maxstrauch/kim-uno/images/backshot.jpg

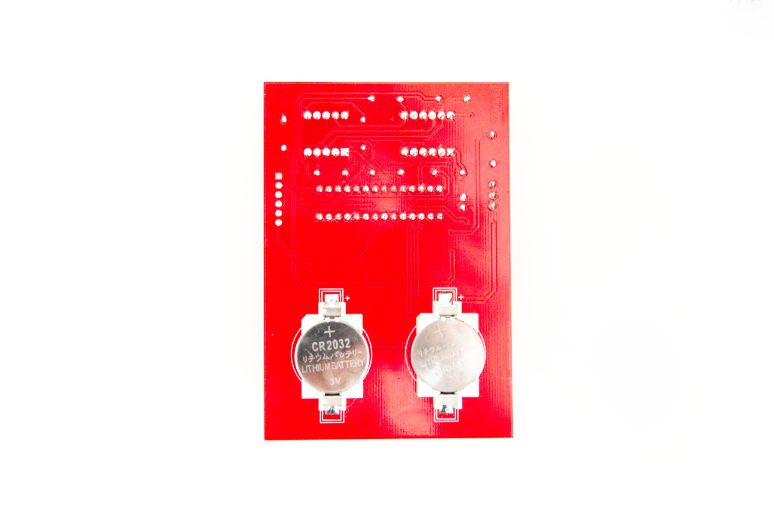
images/backshot.jpg
