maxstrauch/kim-uno/images/family_shot.jpg

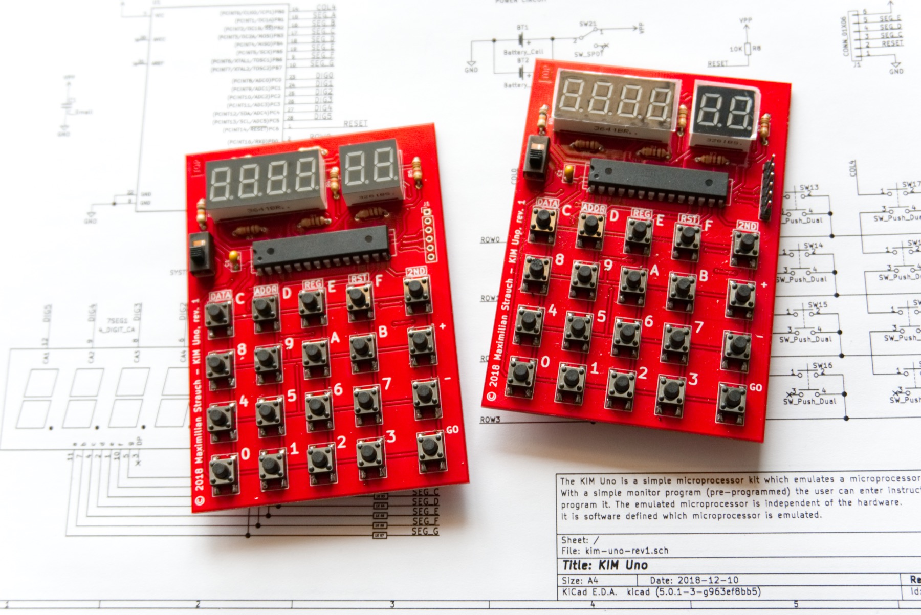
images/family_shot.jpg
