maxstrauch/kim-uno/images/finished_batteries.jpg

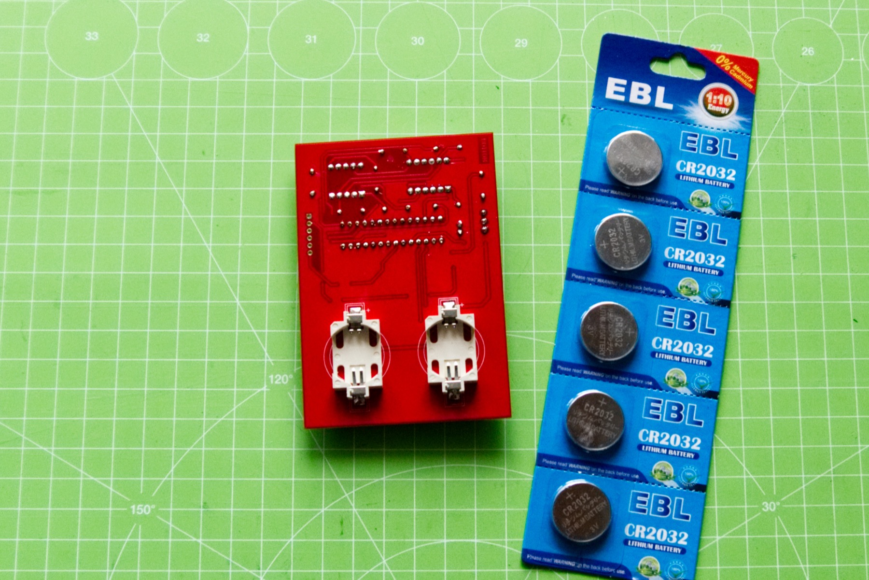
images/finished_batteries.jpg
