maxstrauch/kim-uno/images/finished_product.jpg

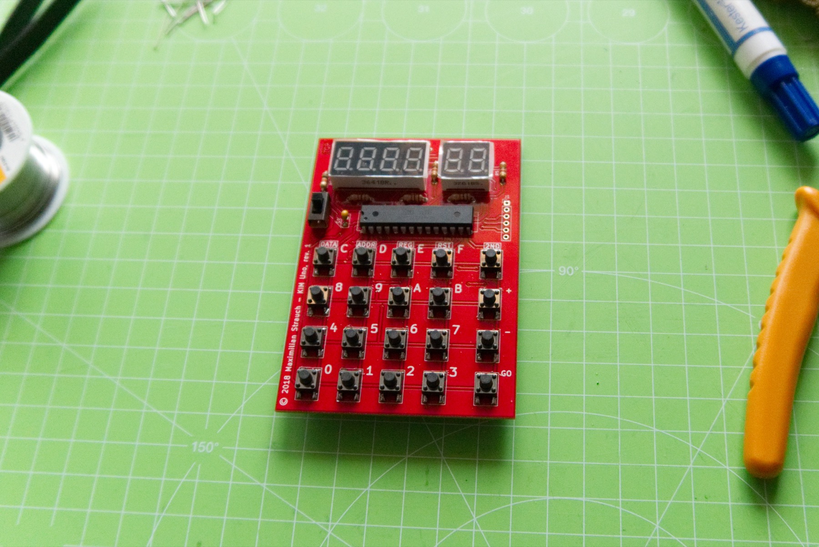
images/finished_product.jpg
