maxstrauch/kim-uno/images/frontshot.jpg

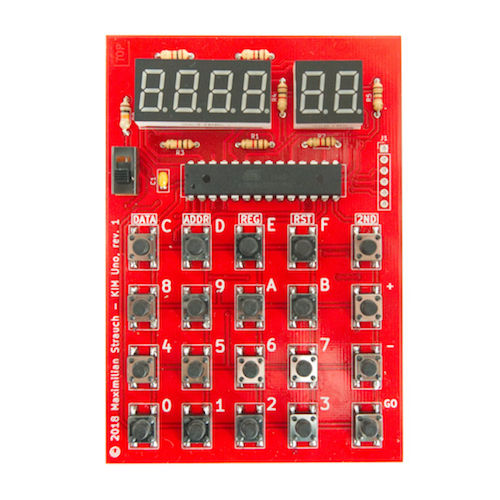
images/frontshot.jpg
