maxstrauch/kim-uno/images/frontshot_bg-plans.jpg

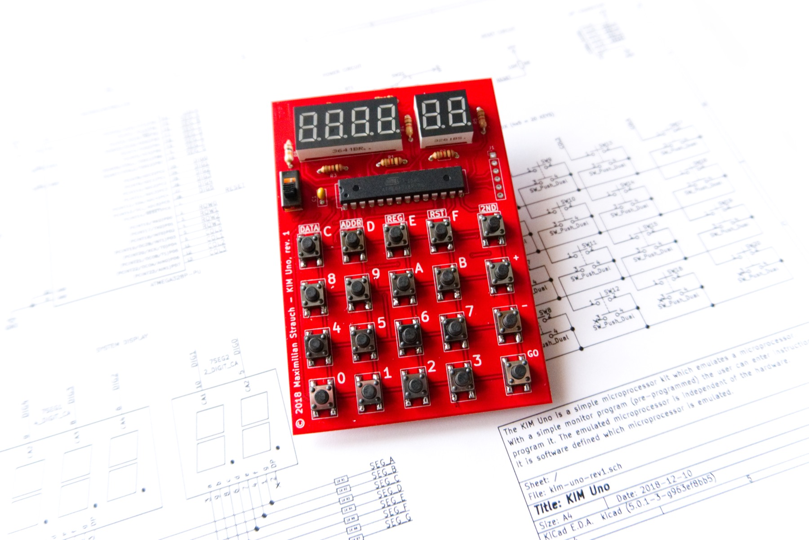
images/frontshot_bg-plans.jpg
