maxstrauch/kim-uno/images/frontshot_with_booklet2.jpg

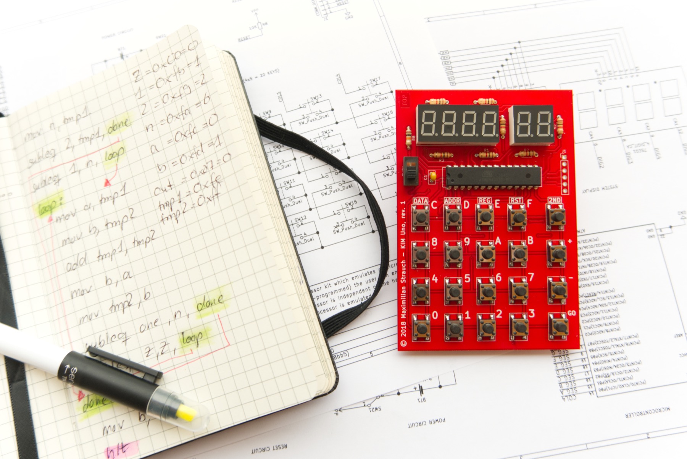
images/frontshot_with_booklet2.jpg
