maxstrauch/kim-uno/images/frontshot_with_booklet.jpg

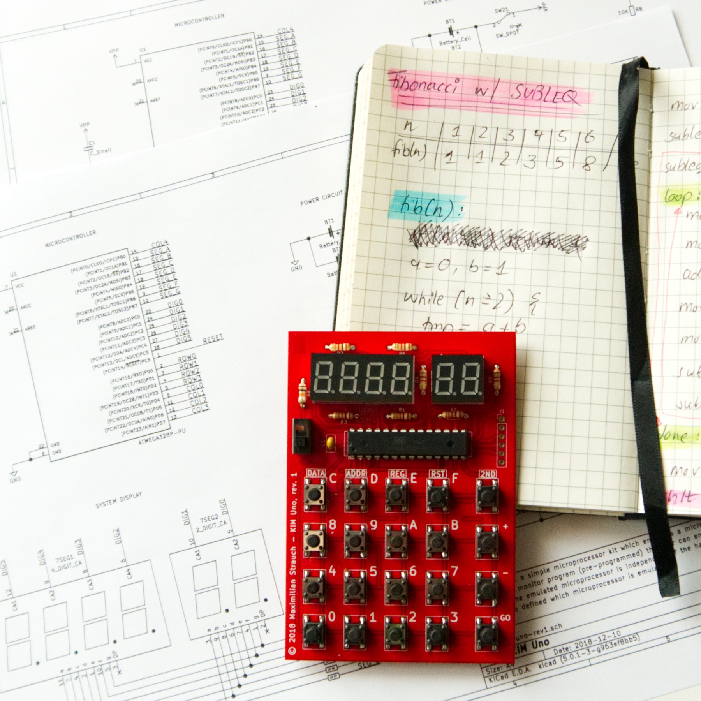
images/frontshot_with_booklet.jpg
