maxstrauch/kim-uno/images/isp_programming.jpg

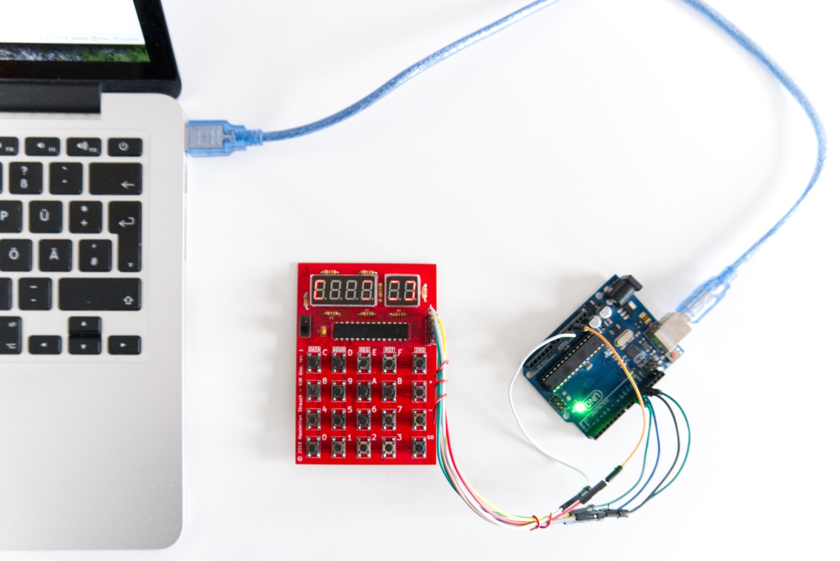
images/isp_programming.jpg
