maxstrauch/kim-uno/images/isp_programming_trick.jpg

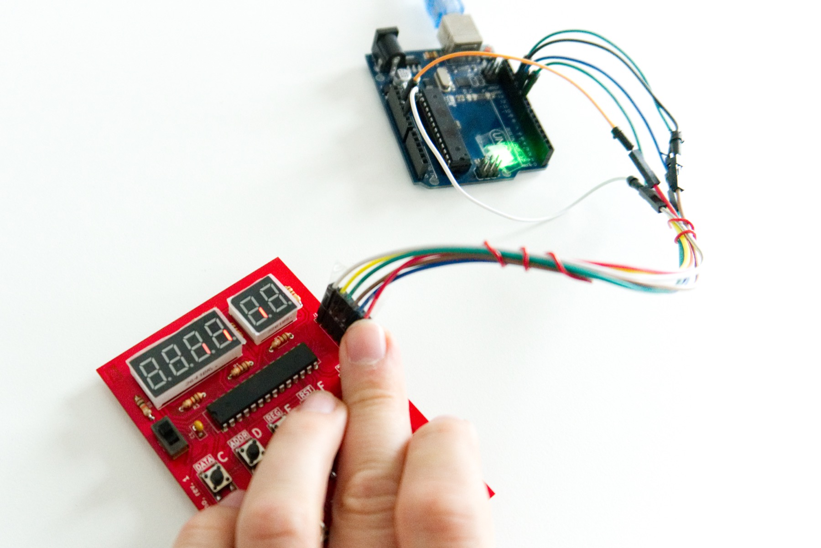
images/isp_programming_trick.jpg
