maxstrauch/kim-uno/images/kim-uno-rev1-schematic.png

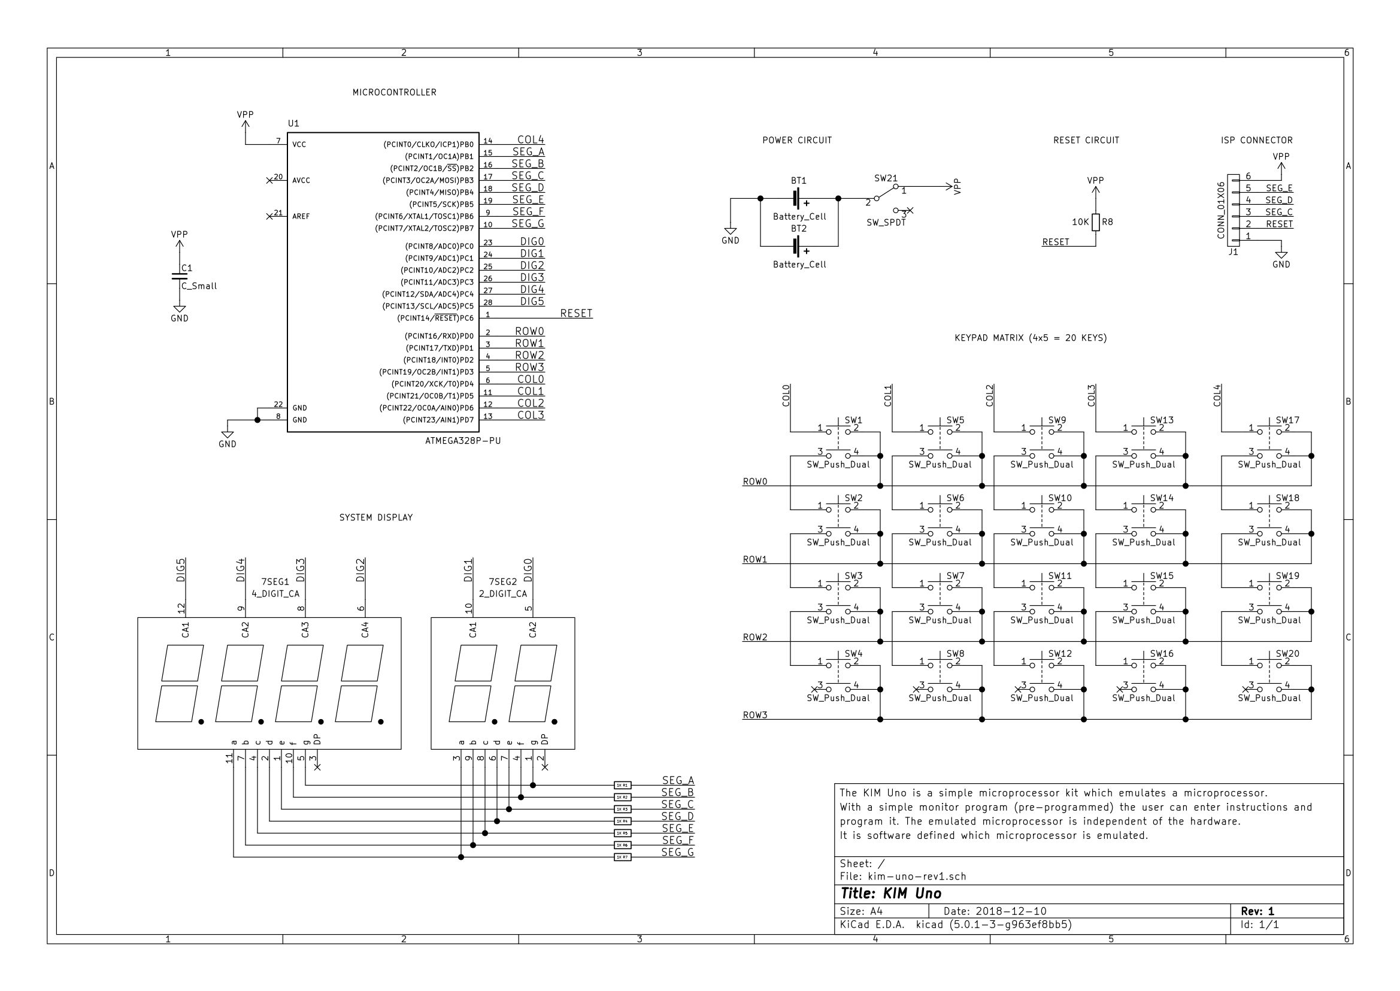
images/kim-uno-rev1-schematic.png
