maxstrauch/kim-uno/images/main-title.jpg

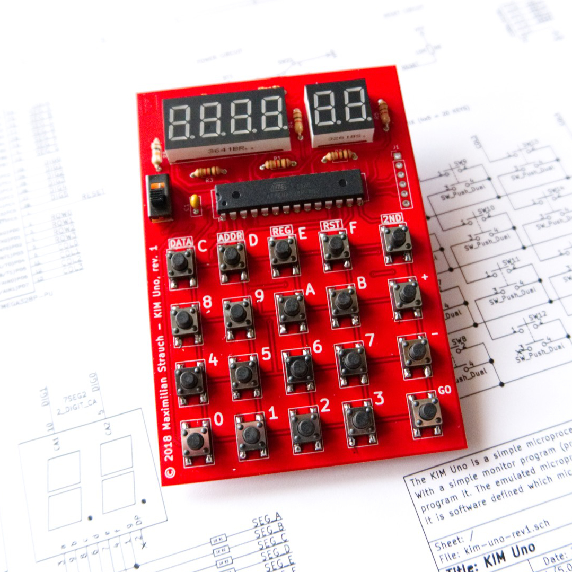
images/main-title.jpg
