maxstrauch/kim-uno/images/pcb.jpg

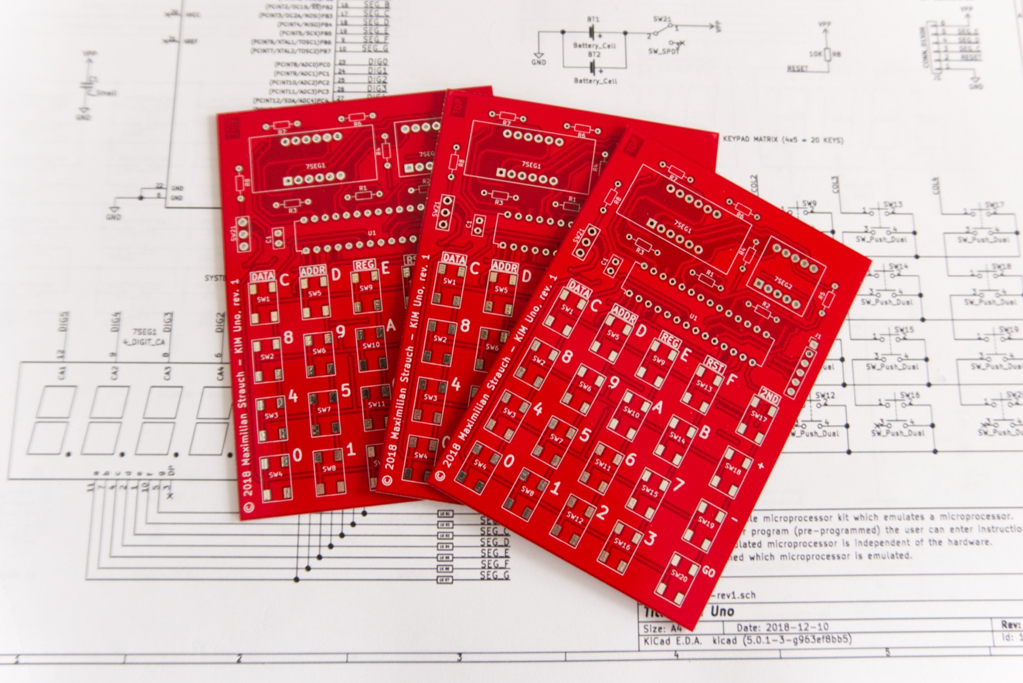
images/pcb.jpg
