maxstrauch/kim-uno/images/screenshot_kicad.png

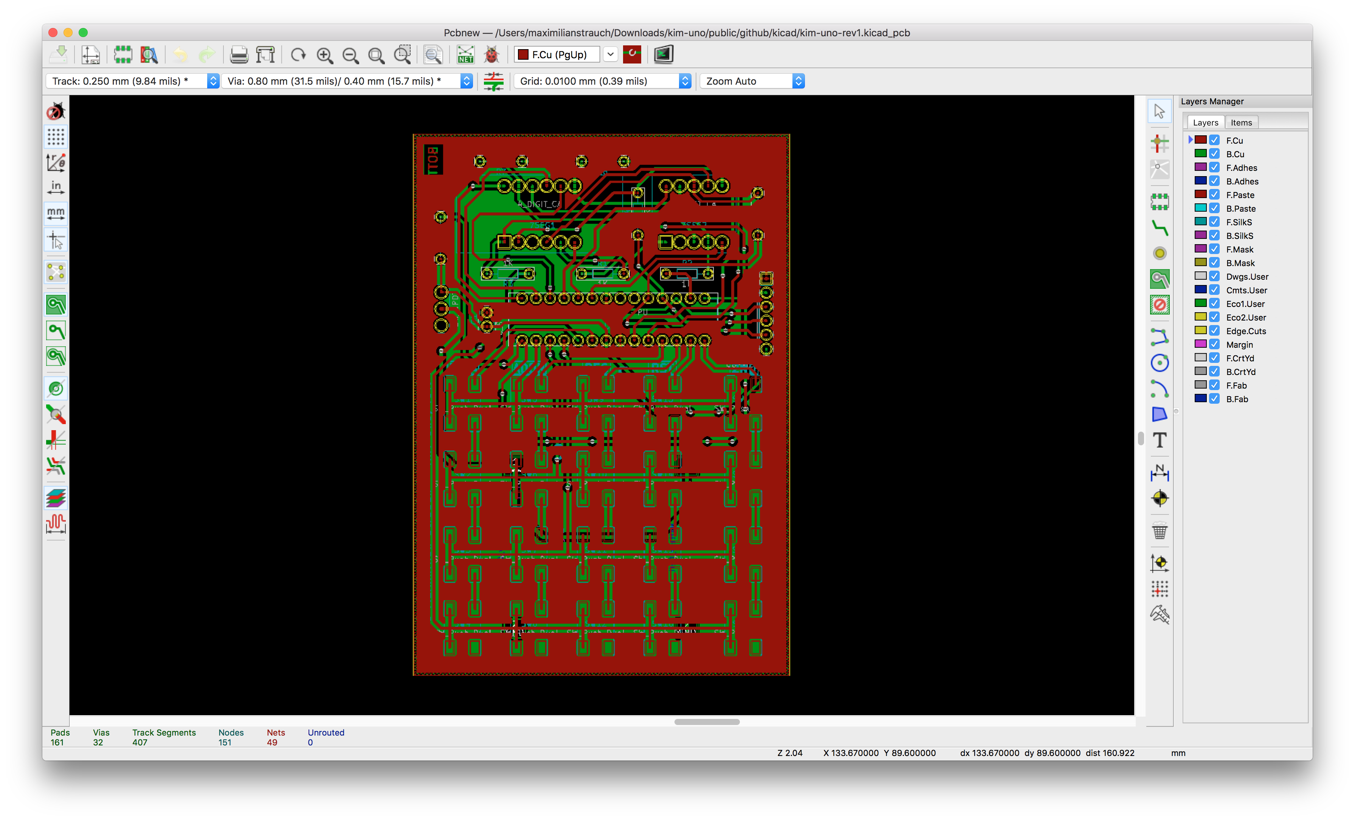
images/screenshot_kicad.png
