maxstrauch/kim-uno/images/tools.jpg

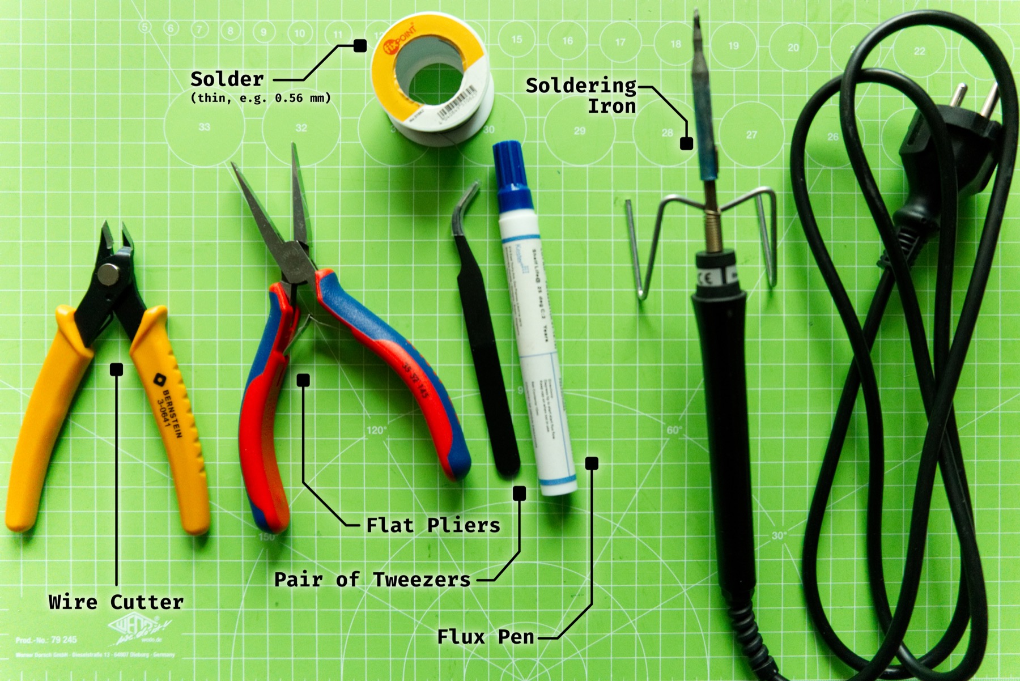
images/tools.jpg
