maxstrauch/kim-uno/kicad/datasheets/B3F-Tact-Switch-6x6x4-3-1000PCS-LOT-push-button-switch-5-6-7-8-9-10.jpg

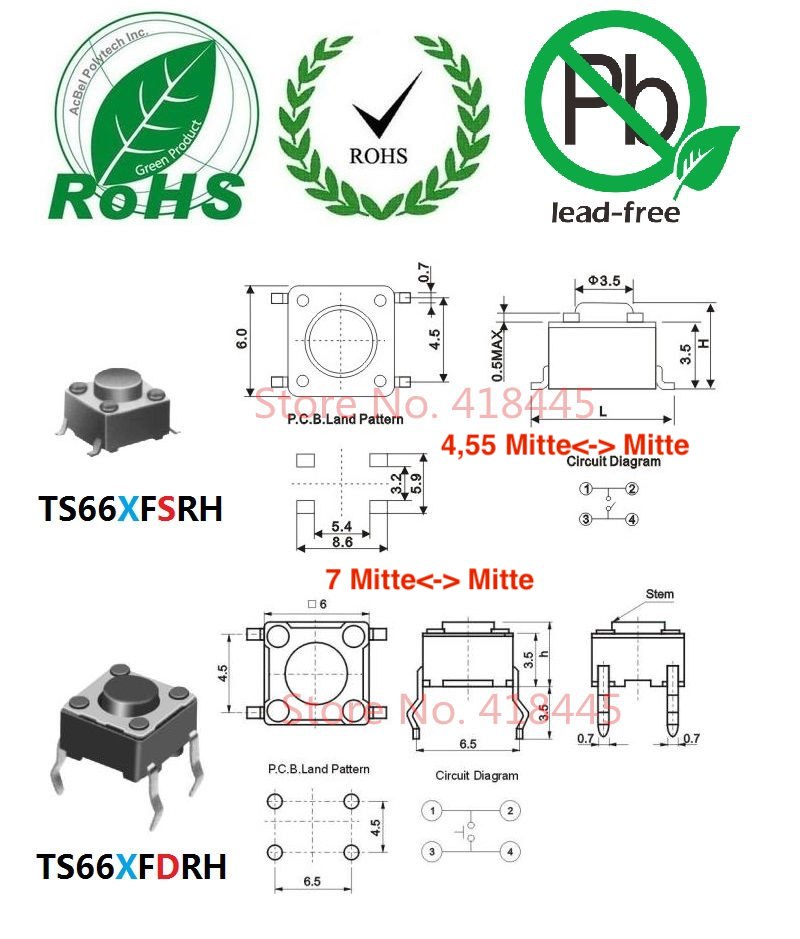
kicad/datasheets/B3F-Tact-Switch-6x6x4-3-1000PCS-LOT-push-button-switch-5-6-7-8-9-10.jpg
