maxstrauch/kim-uno/kicad/datasheets/The-toggle-switch-SS12F17G3-factory-direct-slide-switch-electronic-switch.jpg

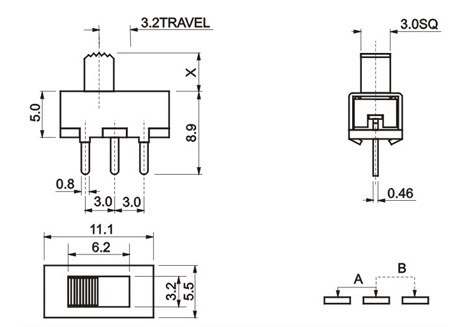
kicad/datasheets/The-toggle-switch-SS12F17G3-factory-direct-slide-switch-electronic-switch.jpg
