maxstrauch/kim-uno/kicad/datasheets/Z1561605.jpg

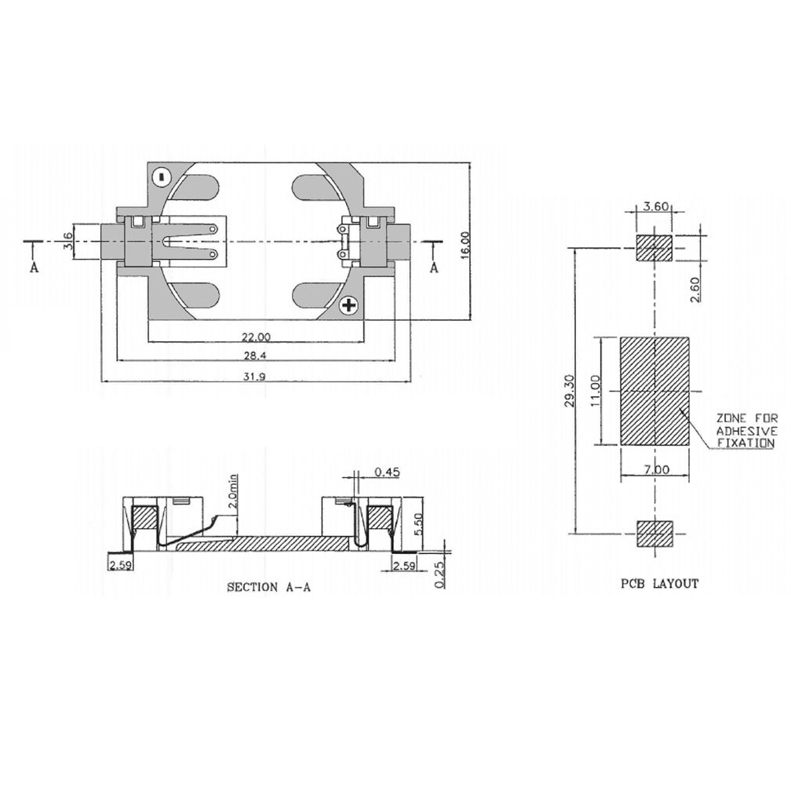
kicad/datasheets/Z1561605.jpg
