maxstrauch/kim-uno/images/step1_resistors.jpg

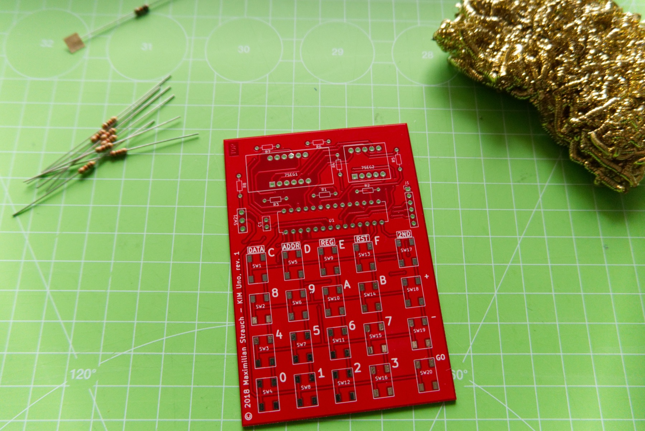
images/step1_resistors.jpg
