maxstrauch/kim-uno/images/step1a_bend_resistors_over.jpg

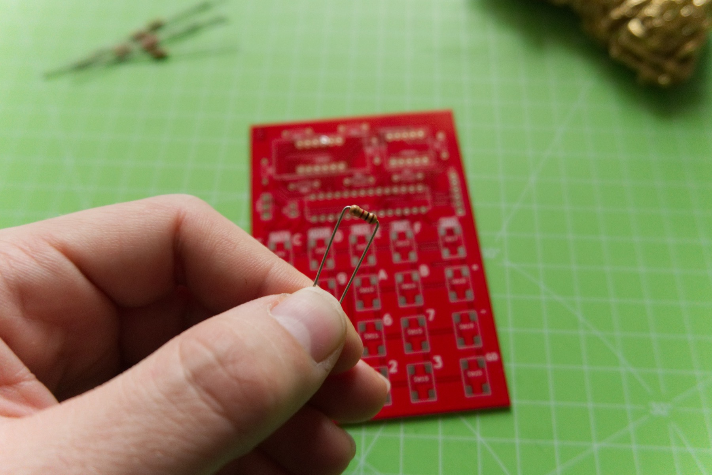
images/step1a_bend_resistors_over.jpg
