maxstrauch/kim-uno/images/step1b_insert_resistors.jpg

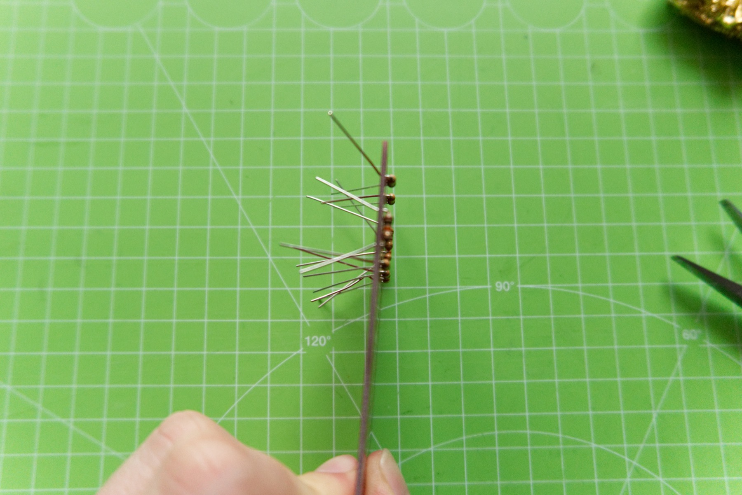
images/step1b_insert_resistors.jpg
