maxstrauch/kim-uno/images/step1c_cut_wires.jpg

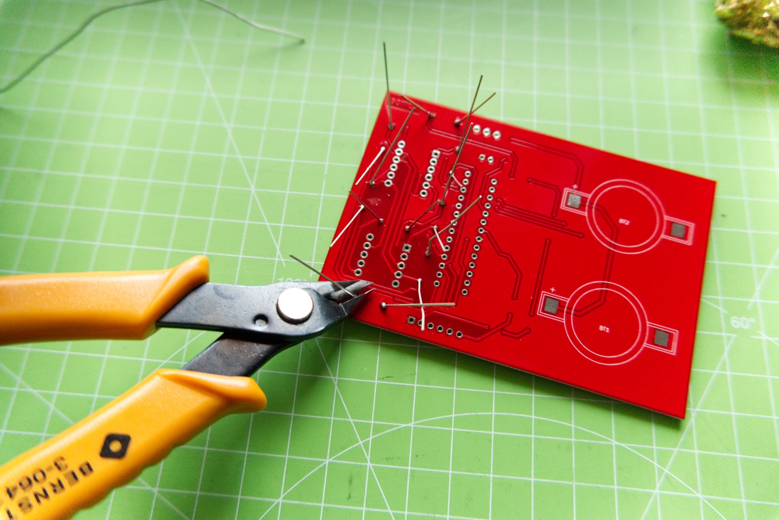
images/step1c_cut_wires.jpg
