maxstrauch/kim-uno/images/step2_assemble_switches.jpg

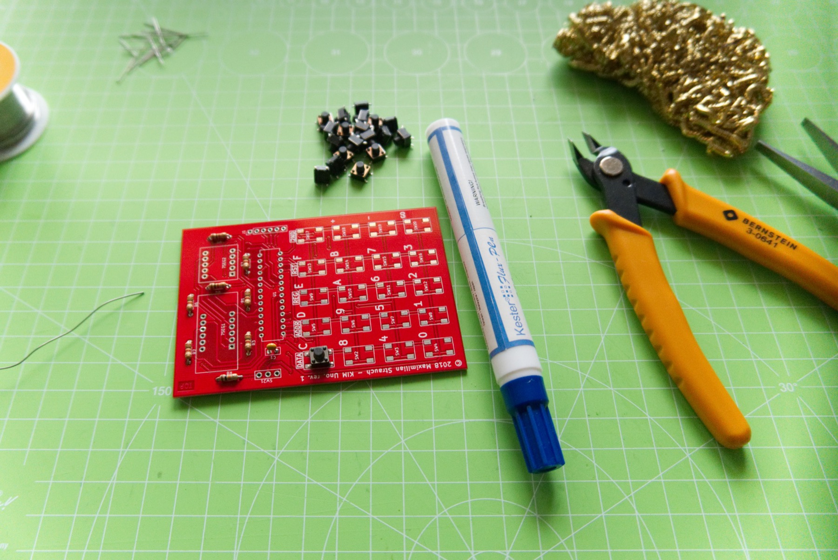
images/step2_assemble_switches.jpg
