maxstrauch/kim-uno/images/step2b_tac_switches_w_labels.jpg

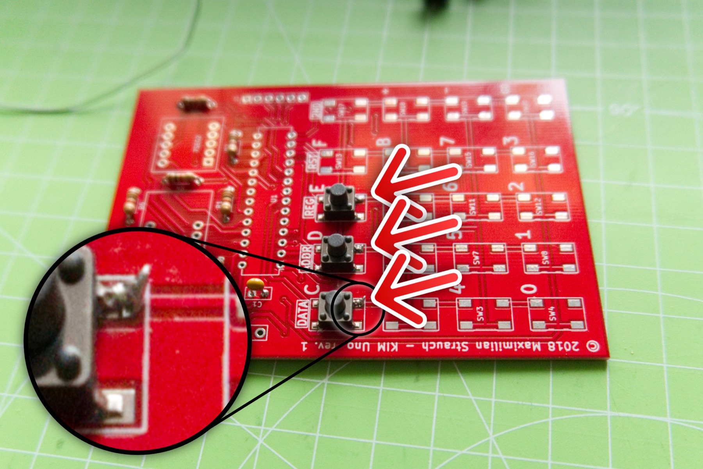
images/step2b_tac_switches_w_labels.jpg
