maxstrauch/kim-uno/images/step2c_finished.jpg

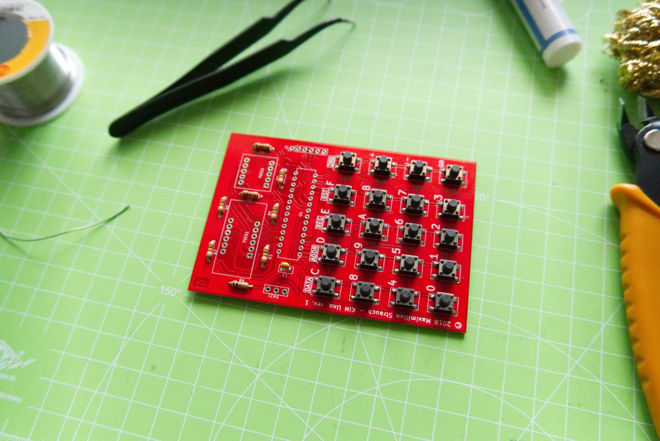
images/step2c_finished.jpg
