maxstrauch/kim-uno/images/step5_install_seven_segment_tac_w_label.jpg

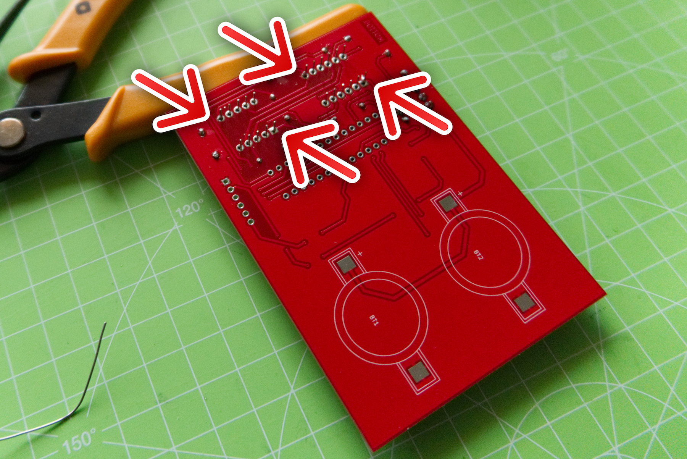
images/step5_install_seven_segment_tac_w_label.jpg
