maxstrauch/kim-uno/images/step5b_then_solder_the_rest.jpg

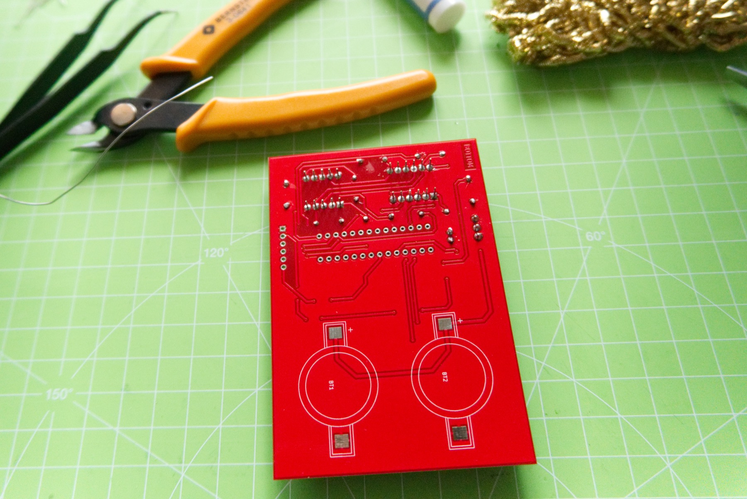
images/step5b_then_solder_the_rest.jpg
