maxstrauch/kim-uno/images/step6_add_battery_holders.jpg

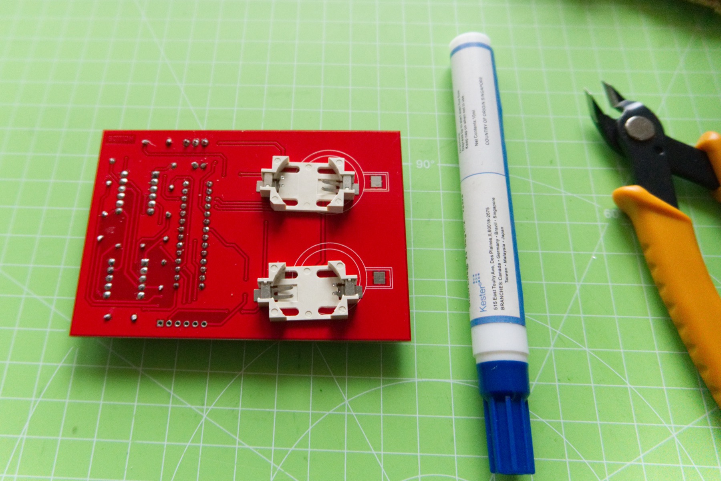
images/step6_add_battery_holders.jpg
