maxstrauch/kim-uno/src/fibonacci.h

/*
 --- Report ---
  Program starts at: 0x0a
  Code length: 96 bytes

  Variables:
   - z at 0x00 (initial value: 0)
   - n at 0xfa (initial value: 6)
   - a at 0xfc (initial value: 0)
   - b at 0xfd (initial value: 1)
   - out at 0x07 (initial value: 0)
   - tmp1 at 0xfe (initial value: 0)
   - tmp2 at 0xff (initial value: 0)
   - one at 0xfb (initial value: 1)
   - two at 0xf9 (initial value: 2)

  Labels:
   - loop at 28
   - done at 91
*/

unsigned const PROGMEM char prg[256] = {
/*        0x00  0x01  0x02  0x03  0x04  0x05  0x06  0x07  0x08  0x09  0x0a  0x0b  0x0c  0x0d  0x0e  0x0f  */
/*0x00*/  0x00, 0x00, 0x00, 0x00, 0x00, 0x00, 0x00, 0x00, 0x00, 0x00, 0xfe, 0xfe, 0x0d, 0xfa, 0x00, 0x10, 
/*0x10*/  0x00, 0xfe, 0x13, 0x00, 0x00, 0x16, 0xf9, 0xfe, 0x5b, 0xfb, 0xfa, 0x1c, 0xfe, 0xfe, 0x1f, 0xfc, 
/*0x20*/  0x00, 0x22, 0x00, 0xfe, 0x25, 0x00, 0x00, 0x28, 0xff, 0xff, 0x2b, 0xfd, 0x00, 0x2e, 0x00, 0xff, 
/*0x30*/  0x31, 0x00, 0x00, 0x34, 0xfe, 0x00, 0x37, 0x00, 0xff, 0x3a, 0x00, 0x00, 0x3d, 0xfc, 0xfc, 0x40, 
/*0x40*/  0xfd, 0x00, 0x43, 0x00, 0xfc, 0x46, 0x00, 0x00, 0x49, 0xfd, 0xfd, 0x4c, 0xff, 0x00, 0x4f, 0x00, 
/*0x50*/  0xfd, 0x52, 0x00, 0x00, 0x55, 0xfb, 0xfa, 0x5b, 0x00, 0x00, 0x1c, 0x07, 0x07, 0x5e, 0xfd, 0x00, 
/*0x60*/  0x61, 0x00, 0x07, 0x64, 0x00, 0x00, 0x67, 0x00, 0x00, 0xff, 0x00, 0x00, 0x00, 0x00, 0x00, 0x00, 
/*0x70*/  0x00, 0x00, 0x00, 0x00, 0x00, 0x00, 0x00, 0x00, 0x00, 0x00, 0x00, 0x00, 0x00, 0x00, 0x00, 0x00, 
/*0x80*/  0x00, 0x00, 0x00, 0x00, 0x00, 0x00, 0x00, 0x00, 0x00, 0x00, 0x00, 0x00, 0x00, 0x00, 0x00, 0x00, 
/*0x90*/  0x00, 0x00, 0x00, 0x00, 0x00, 0x00, 0x00, 0x00, 0x00, 0x00, 0x00, 0x00, 0x00, 0x00, 0x00, 0x00, 
/*0xa0*/  0x00, 0x00, 0x00, 0x00, 0x00, 0x00, 0x00, 0x00, 0x00, 0x00, 0x00, 0x00, 0x00, 0x00, 0x00, 0x00, 
/*0xb0*/  0x00, 0x00, 0x00, 0x00, 0x00, 0x00, 0x00, 0x00, 0x00, 0x00, 0x00, 0x00, 0x00, 0x00, 0x00, 0x00, 
/*0xc0*/  0x00, 0x00, 0x00, 0x00, 0x00, 0x00, 0x00, 0x00, 0x00, 0x00, 0x00, 0x00, 0x00, 0x00, 0x00, 0x00, 
/*0xd0*/  0x00, 0x00, 0x00, 0x00, 0x00, 0x00, 0x00, 0x00, 0x00, 0x00, 0x00, 0x00, 0x00, 0x00, 0x00, 0x00, 
/*0xe0*/  0x00, 0x00, 0x00, 0x00, 0x00, 0x00, 0x00, 0x00, 0x00, 0x00, 0x00, 0x00, 0x00, 0x00, 0x00, 0x00, 
/*0xf0*/  0x00, 0x00, 0x00, 0x00, 0x00, 0x00, 0x00, 0x00, 0x00, 0x02, 0x06, 0x01, 0x00, 0x01, 0x00, 0x00, 
};
